GaetanCoraboeuf/capteur_IR/src/wifi_credentials.h

#ifndef WIFI_CREDENTIALS_H
#define WIFI_CREDENTIALS_H
// WiFi credentials for the ESP32

const char* ssid     = "*********"; // Replace with your network SSID
const char* password = "*******************"; // Replace with your network password

#endif
